cep-sose2023/athena-security/05-Supporting-Files/circuit diagram.png

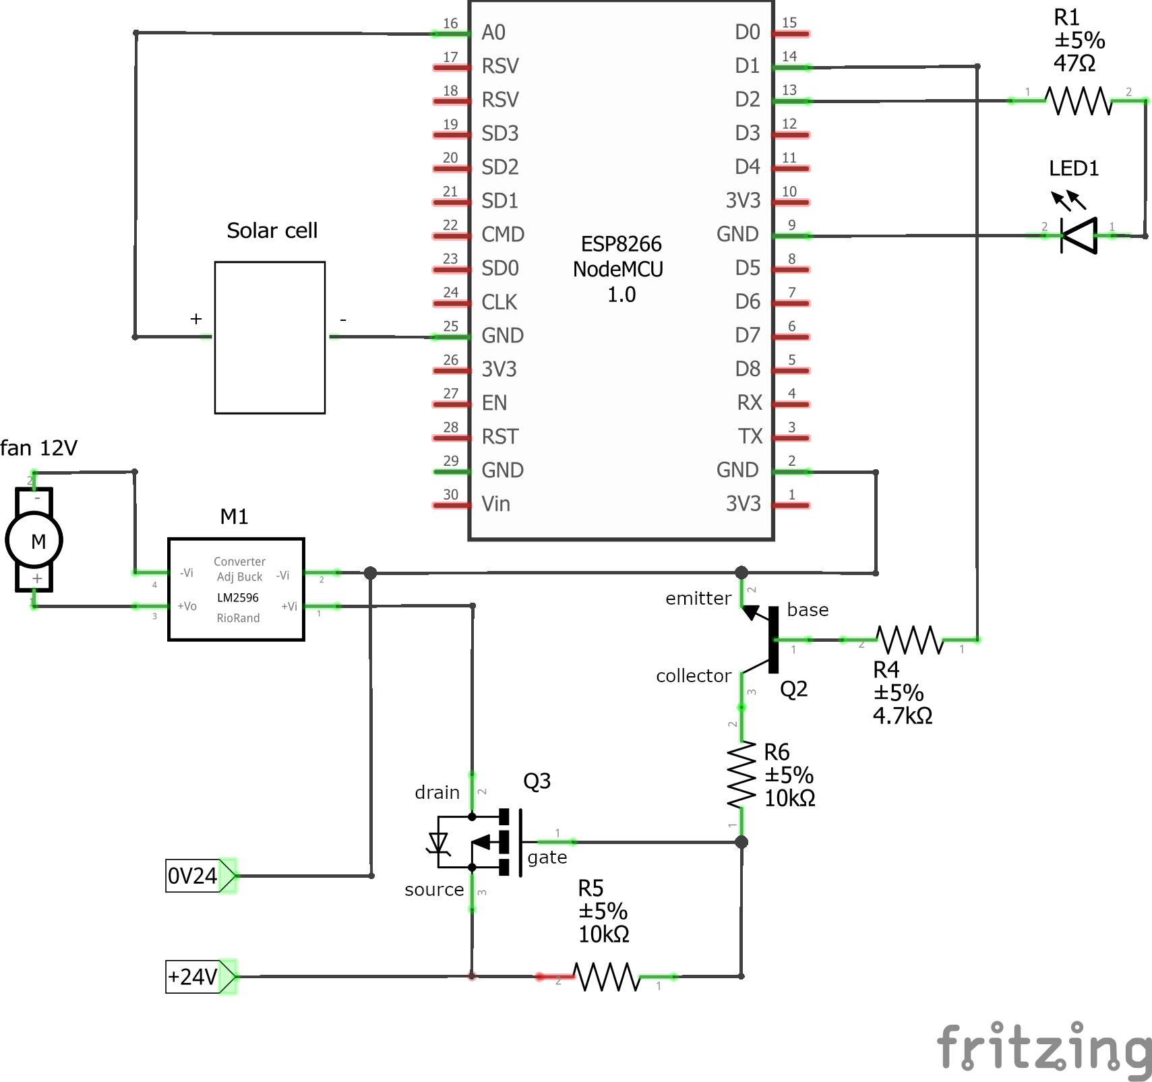
05-Supporting-Files/circuit diagram.png
