cep-sose2023/athena-security/05-Supporting-Files/pattern.jpeg

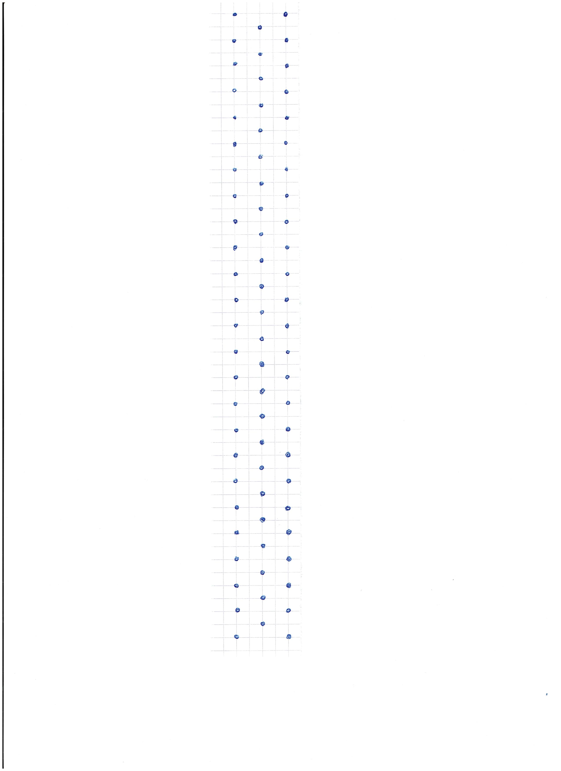
05-Supporting-Files/pattern.jpeg
