cep-sose2023/athena-security/01-Documentation/01-UserGuide/diagrams/component_diagram.png

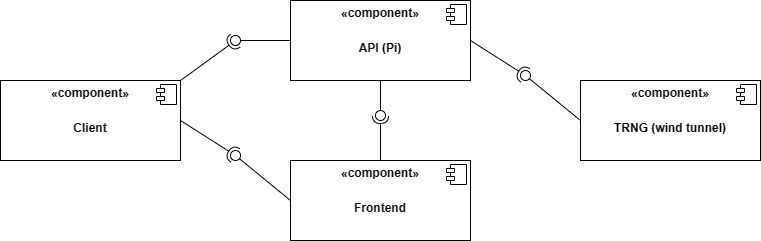
01-Documentation/01-UserGuide/diagrams/component_diagram.png
