cep-sose2023/athena-security/01-Documentation/01-UserGuide/screenshots/frontend/system_page.PNG

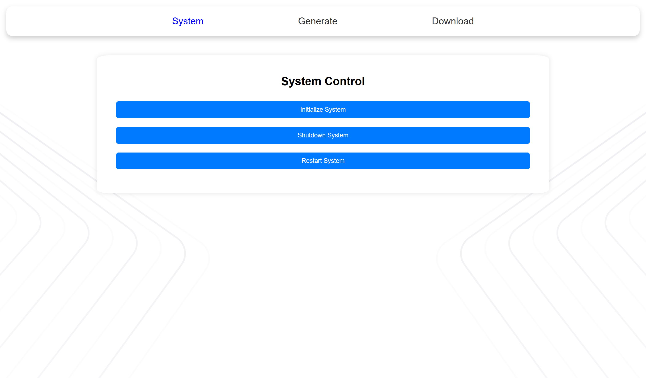
01-Documentation/01-UserGuide/screenshots/frontend/system_page.PNG
