cep-sose2023/athena-security/01-Documentation/01-UserGuide/screenshots/math/expected_value.PNG

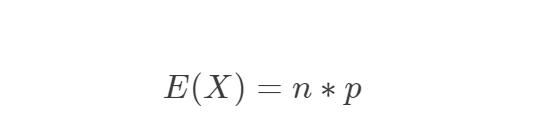
01-Documentation/01-UserGuide/screenshots/math/expected_value.PNG
